AmanRV/STMScope/Core/Inc/pixel.h

/*
 * pixel.h
 *
 *  Created on: Aug 22, 2024
 *      Author: Aman
 */

#ifndef INC_PIXEL_H_
#define INC_PIXEL_H_

typedef struct {
    int x;
    int y;
    int color;
} Pixel;

#endif /* INC_PIXEL_H_ */
